haneefmubarak/satnogs-rotator/cover/cover_side_mirror.fcstd

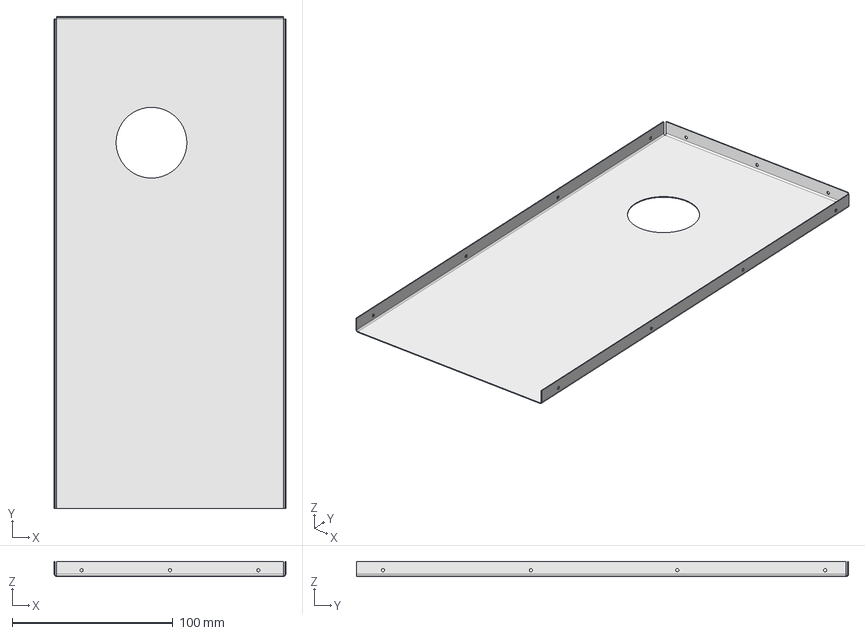
[picture p15: CAD file, 2017-07-28]
cover/cover_side_mirror.fcstd
144.0 x 306.0 x 9.50 mm
