haneefmubarak/satnogs-rotator/rotator_parts/worm_mount.fcstd

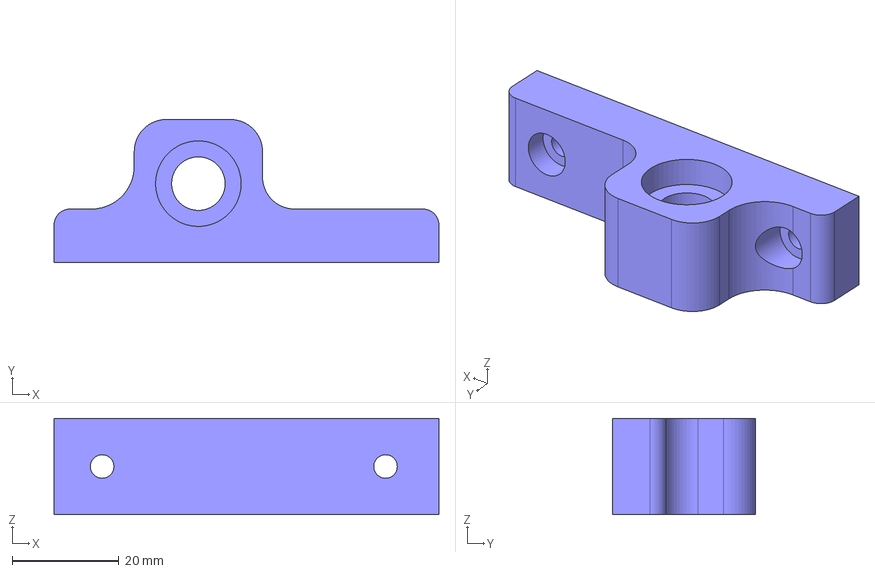
[picture p16: CAD file, 2017-07-28]
rotator_parts/worm_mount.fcstd
72.0 x 26.8 x 18.0 mm
