haneefmubarak/satnogs-rotator/shared/ball_bearing_623ZZ.fcstd

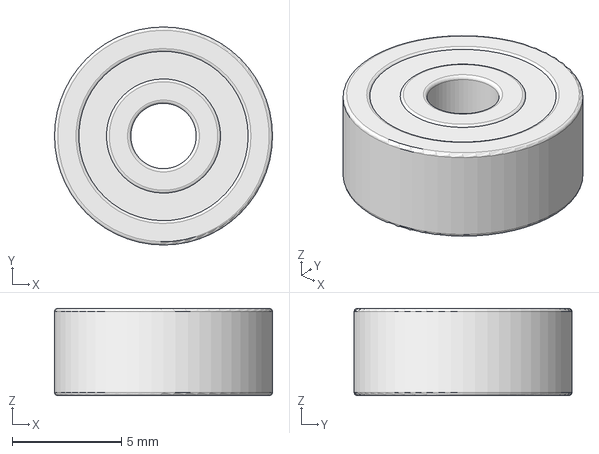
[picture p17: CAD file, 2017-07-28]
shared/ball_bearing_623ZZ.fcstd
10.0 x 10.0 x 4.00 mm
