haneefmubarak/satnogs-rotator/cover/cover_bottom.fcstd

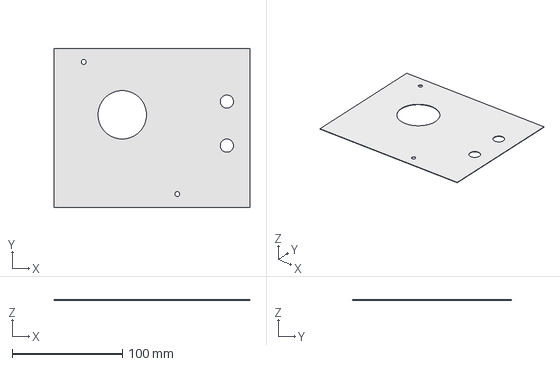
[picture p18: CAD file, 2017-07-28]
cover/cover_bottom.fcstd
178.0 x 144.0 x 0.5 mm
