haneefmubarak/satnogs-rotator/electronics/holder_as5601.fcstd

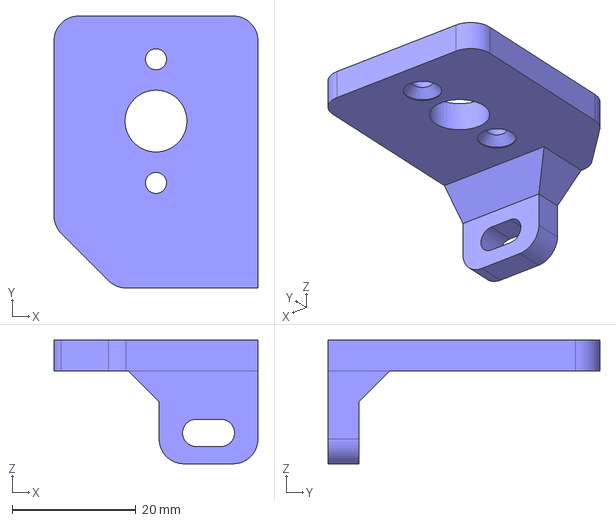
[picture p19: CAD file, 2017-07-28]
electronics/holder_as5601.fcstd
33.0 x 44.0 x 20.0 mm
