haneefmubarak/satnogs-rotator/rotator_parts/axis_gear_flange.fcstd

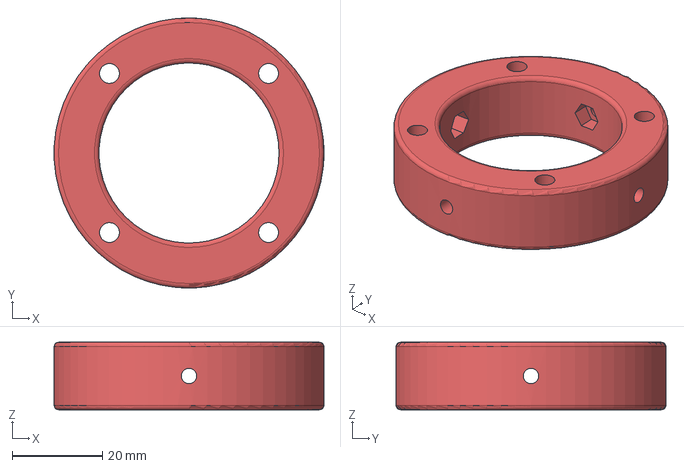
[picture p20: CAD file, 2017-07-28]
rotator_parts/axis_gear_flange.fcstd
60.0 x 60.0 x 15.0 mm
