haneefmubarak/satnogs-rotator/cover/rain_cover_tube.fcstd

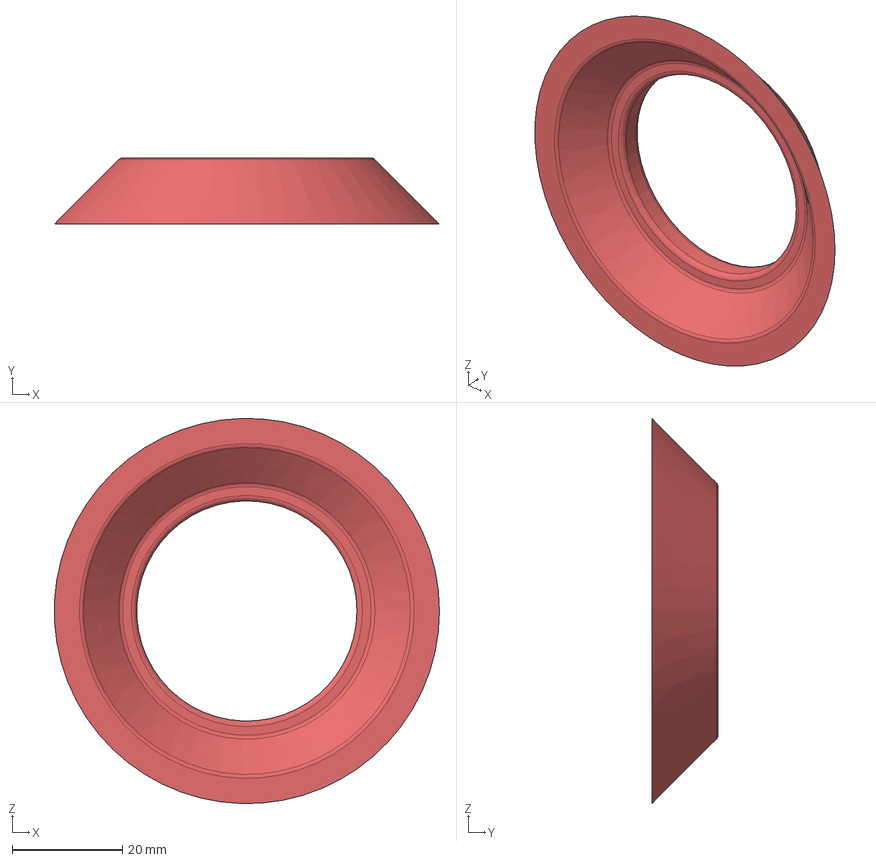
[picture p21: CAD file, 2017-07-28]
cover/rain_cover_tube.fcstd
70.0 x 12.0 x 70.0 mm
