haneefmubarak/satnogs-rotator/electronics/electronics_case_pcb_mount.fcstd

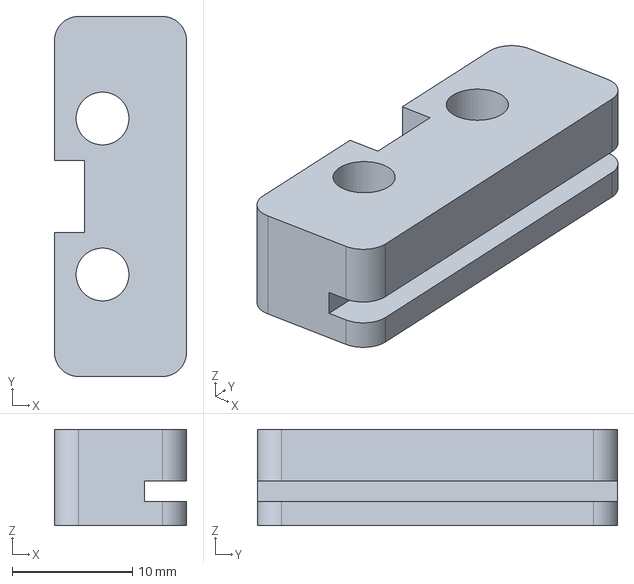
[picture p22: CAD file, 2017-07-28]
electronics/electronics_case_pcb_mount.fcstd
11.0 x 30.0 x 8.00 mm
