haneefmubarak/satnogs-rotator/rotator_parts/t_slot20_100.fcstd

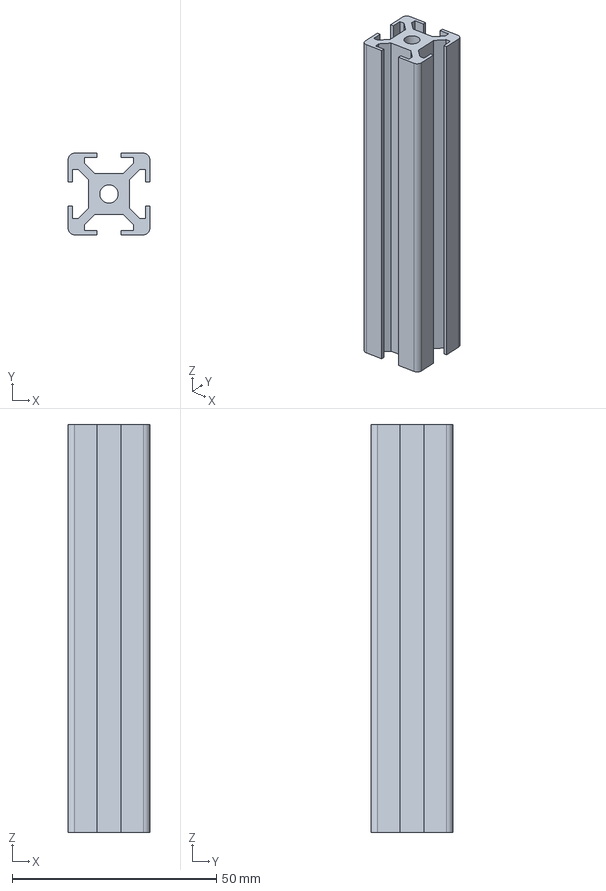
[picture p23: CAD file, 2017-07-28]
rotator_parts/t_slot20_100.fcstd
20.0 x 20.0 x 100.0 mm
