haneefmubarak/satnogs-rotator/shared/standoff_hex_nylon_M3_L10_ff.fcstd

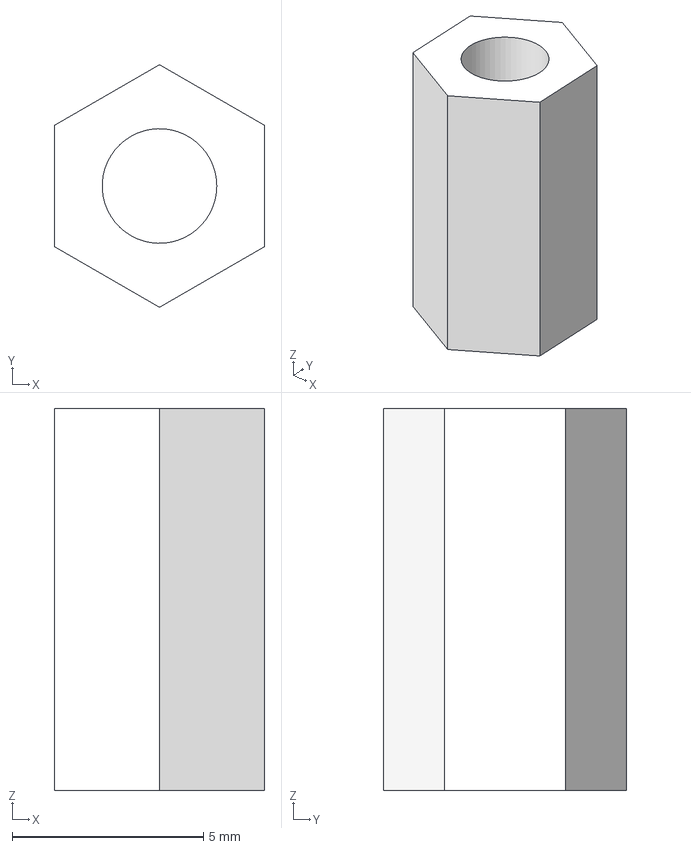
[picture p24: CAD file, 2017-07-28]
shared/standoff_hex_nylon_M3_L10_ff.fcstd
5.50 x 6.35 x 10.0 mm
