haneefmubarak/satnogs-rotator/electronics/off_axis_gear_as5601.fcstd

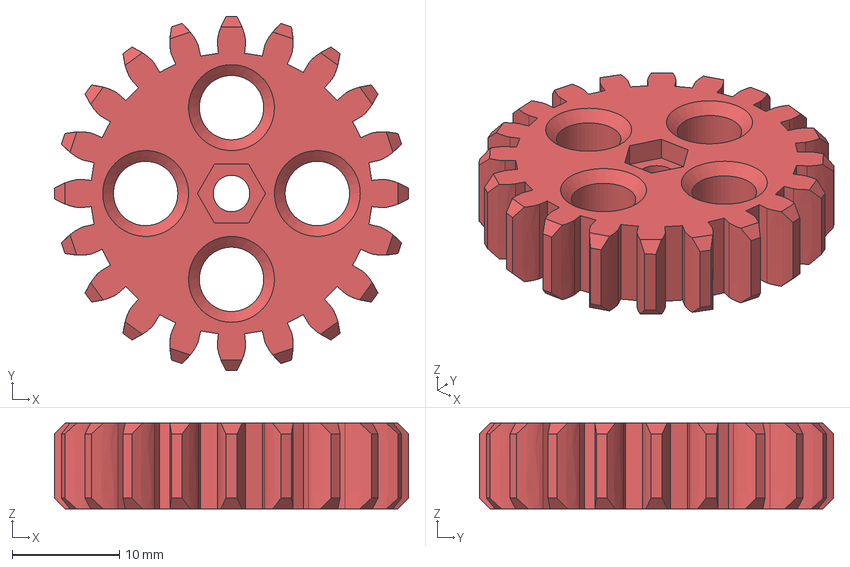
[picture p25: CAD file, 2017-07-28]
electronics/off_axis_gear_as5601.fcstd
33.0 x 33.0 x 8.00 mm
