haneefmubarak/satnogs-rotator/rotator_parts/dc_motor_cup.fcstd

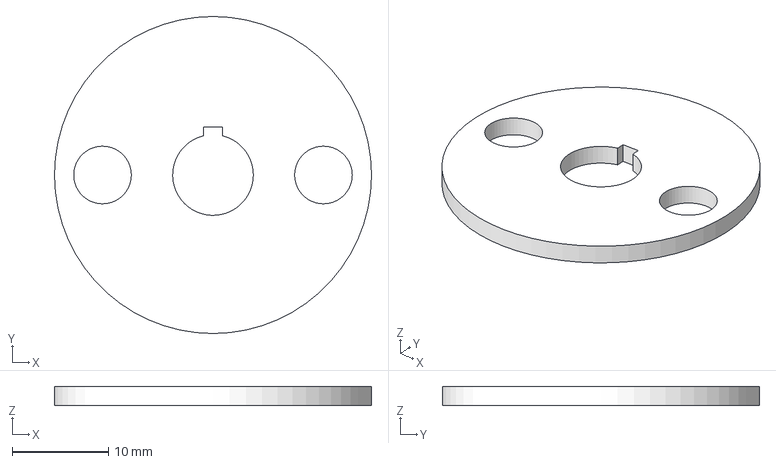
[picture p26: CAD file, 2017-07-28]
rotator_parts/dc_motor_cup.fcstd
33.0 x 33.0 x 2.00 mm
