haneefmubarak/satnogs-rotator/shared/ball_bearing_6008ZZ.fcstd

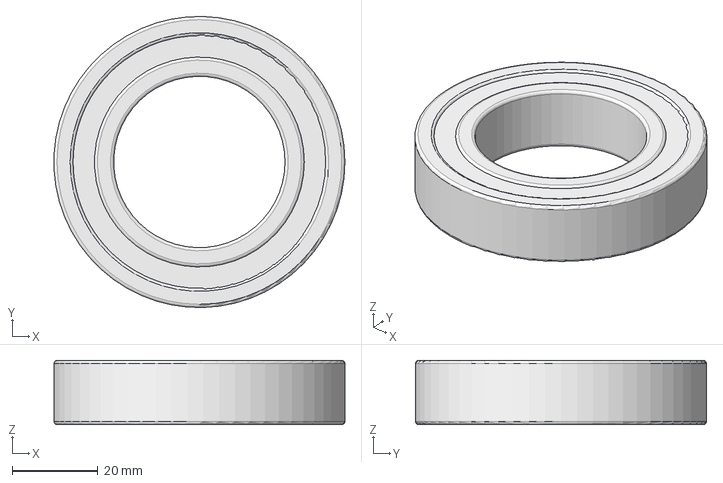
[picture p27: CAD file, 2017-07-28]
shared/ball_bearing_6008ZZ.fcstd
67.9 x 68.0 x 15.0 mm
