haneefmubarak/satnogs-rotator/electronics/encoder_magnet.fcstd

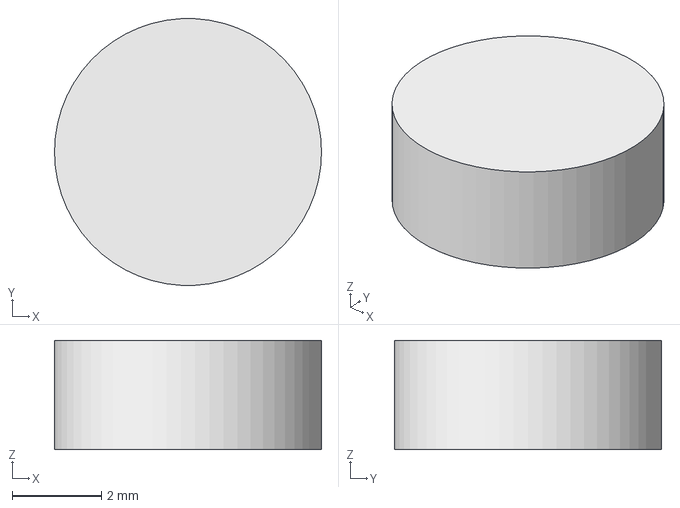
[picture p28: CAD file, 2017-07-28]
electronics/encoder_magnet.fcstd
6.00 x 5.99 x 2.45 mm
