haneefmubarak/satnogs-rotator/rotator_parts/worm_gear.fcstd

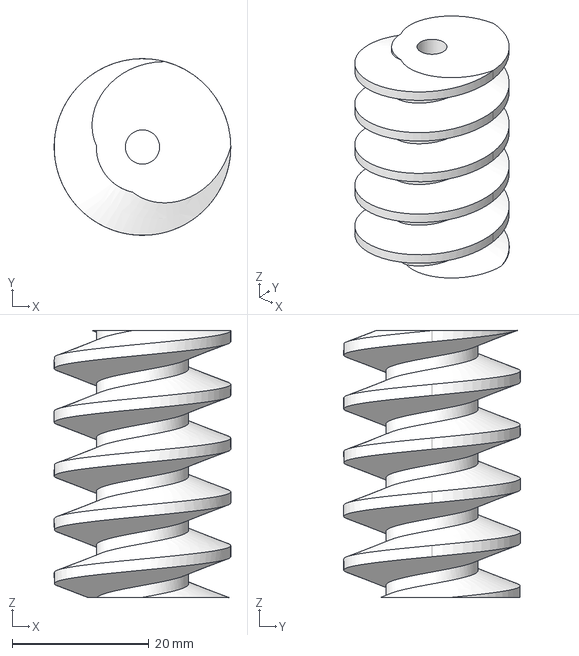
[picture p29: CAD file, 2017-07-28]
rotator_parts/worm_gear.fcstd
25.8 x 25.8 x 39.0 mm
