haneefmubarak/satnogs-rotator/shared/ball_bearing_625ZZ.fcstd

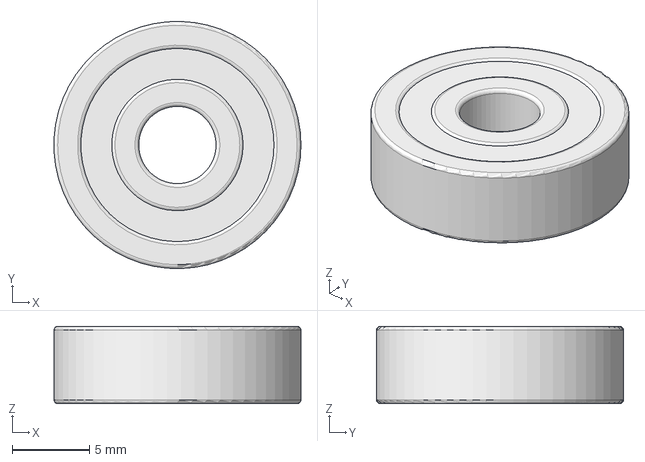
[picture p30: CAD file, 2017-07-28]
shared/ball_bearing_625ZZ.fcstd
16.0 x 16.0 x 5.00 mm
