haneefmubarak/satnogs-rotator/electronics/as5601_case_3.fcstd

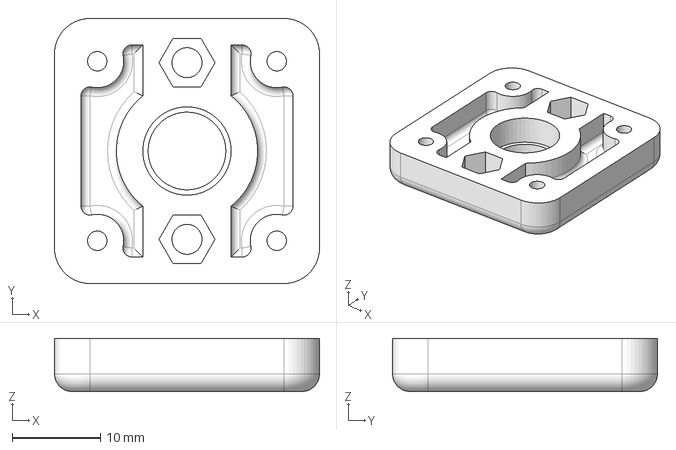
[picture p31: CAD file, 2017-07-28]
electronics/as5601_case_3.fcstd
30.0 x 30.0 x 6.00 mm
