haneefmubarak/satnogs-rotator/rotator_parts/t_slot20_connector.fcstd

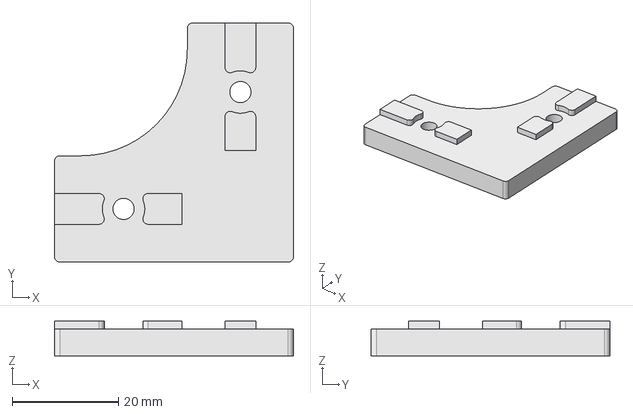
[picture p32: CAD file, 2017-07-28]
rotator_parts/t_slot20_connector.fcstd
45.0 x 45.0 x 6.50 mm
