haneefmubarak/satnogs-rotator/shared/motor_mount.fcstd

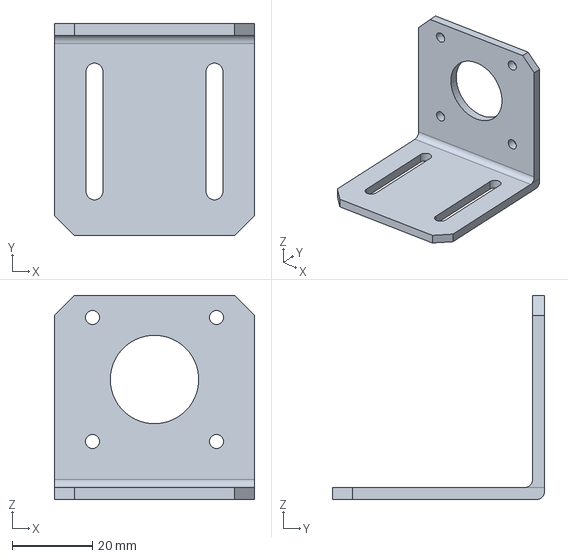
[picture p33: CAD file, 2017-07-28]
shared/motor_mount.fcstd
50.0 x 53.0 x 51.0 mm
