haneefmubarak/satnogs-rotator/electronics/as5601_pcb.fcstd

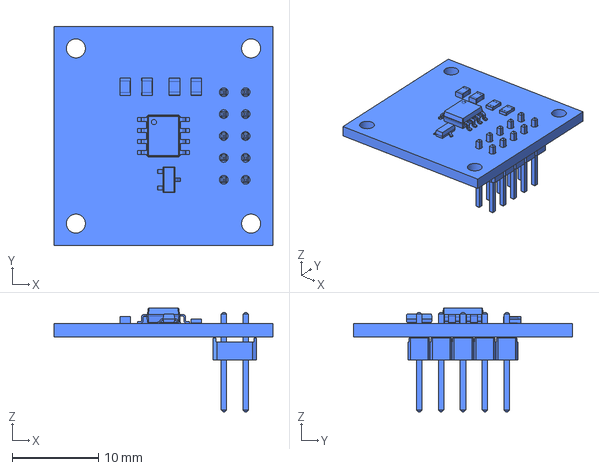
[picture p34: CAD file, 2017-07-28]
electronics/as5601_pcb.fcstd
25.4 x 25.4 x 12.0 mm
