haneefmubarak/satnogs-rotator/rotator_parts/worm_axis.fcstd

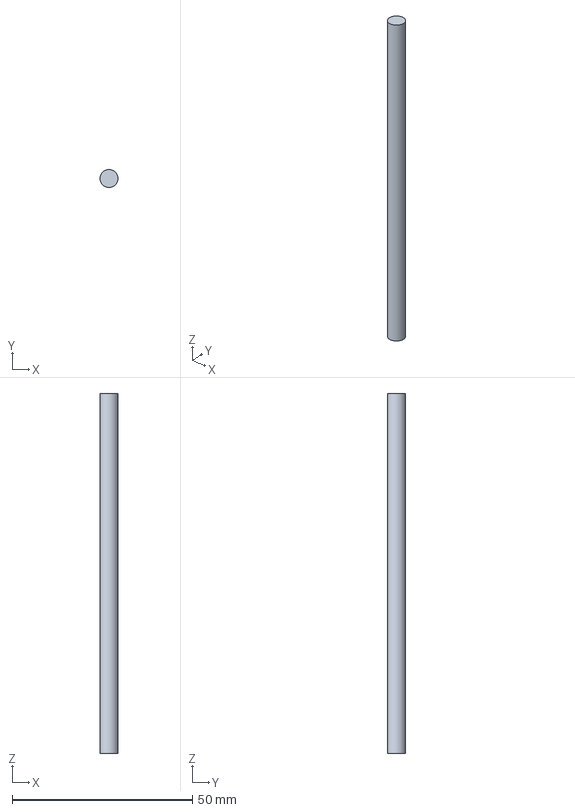
[picture p35: CAD file, 2017-07-28]
rotator_parts/worm_axis.fcstd
5.00 x 5.00 x 100.0 mm
