haneefmubarak/satnogs-rotator/shared/timing_pulley_gt2_36T.fcstd

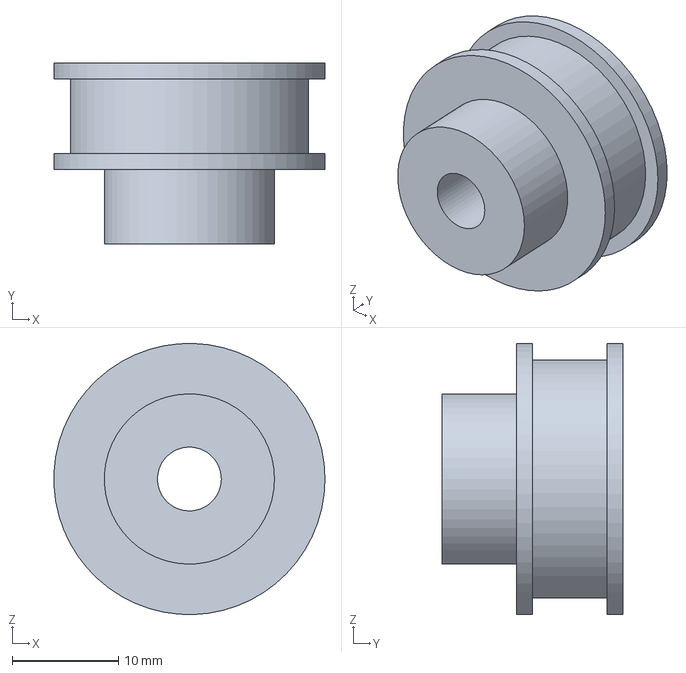
[picture p36: CAD file, 2017-07-28]
shared/timing_pulley_gt2_36T.fcstd
25.5 x 17.0 x 25.5 mm
