haneefmubarak/satnogs-rotator/rotator_parts/motor_mount_flange.fcstd

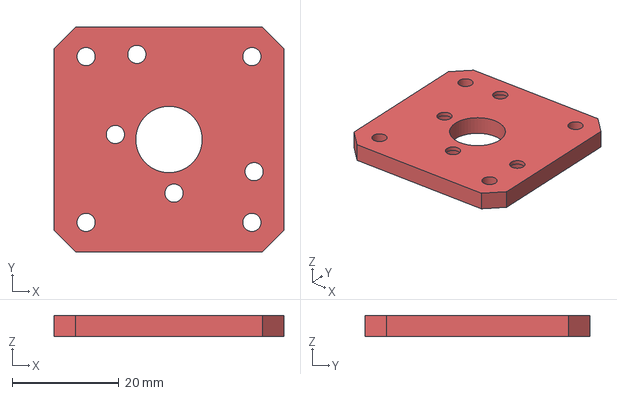
[picture p37: CAD file, 2017-07-28]
rotator_parts/motor_mount_flange.fcstd
43.0 x 42.0 x 4.00 mm
