haneefmubarak/satnogs-rotator/shared/timing_pulley_gt2_20T.fcstd

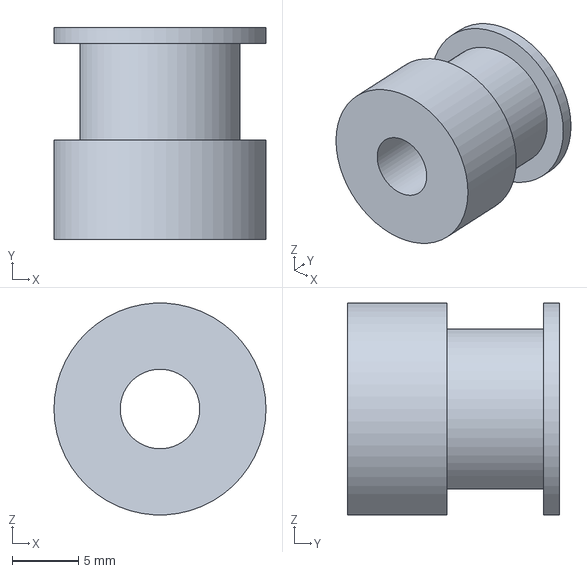
[picture p38: CAD file, 2017-07-28]
shared/timing_pulley_gt2_20T.fcstd
16.0 x 16.0 x 16.0 mm
