haneefmubarak/satnogs-rotator/electronics/as5601_case_2.fcstd

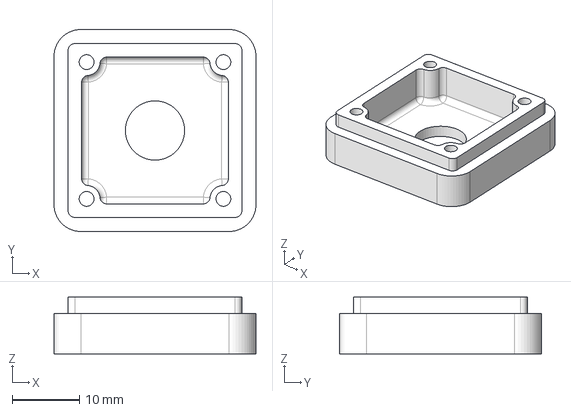
[picture p39: CAD file, 2017-07-28]
electronics/as5601_case_2.fcstd
30.0 x 30.0 x 8.40 mm
