haneefmubarak/satnogs-rotator/rotator_parts/dc_motor_heatshrink.fcstd

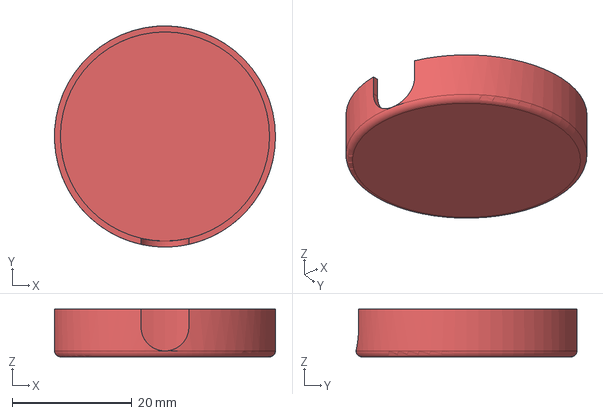
[picture p40: CAD file, 2017-07-28]
rotator_parts/dc_motor_heatshrink.fcstd
37.0 x 37.0 x 8.00 mm
