haneefmubarak/satnogs-rotator/shared/dc_motor_50:1.fcstd

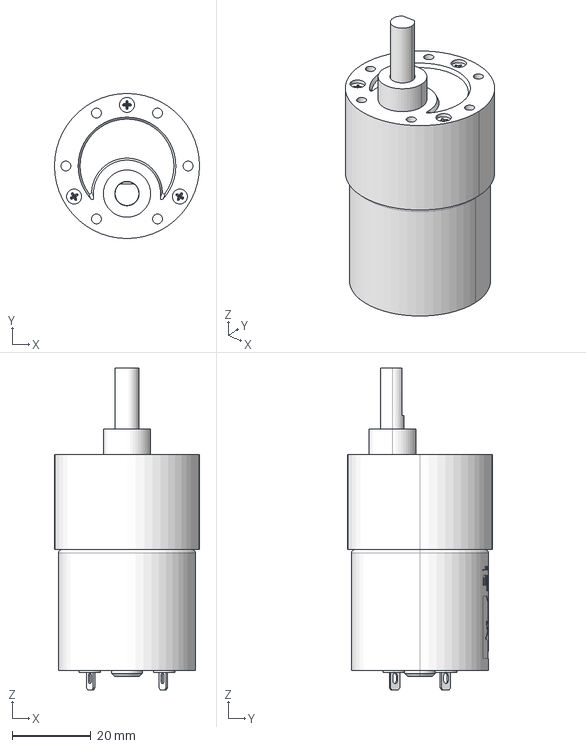
[picture p41: CAD file, 2017-07-28]
shared/dc_motor_50:1.fcstd
36.8 x 36.8 x 81.7 mm
