haneefmubarak/satnogs-rotator/electronics/electronics_case_top.fcstd

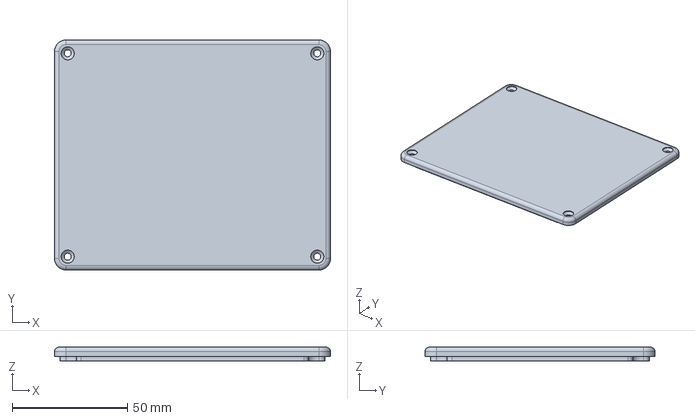
[picture p42: CAD file, 2017-07-28]
electronics/electronics_case_top.fcstd
120.0 x 100.0 x 6.00 mm
