haneefmubarak/satnogs-rotator/rotator_parts/ball_bearing_housing.fcstd

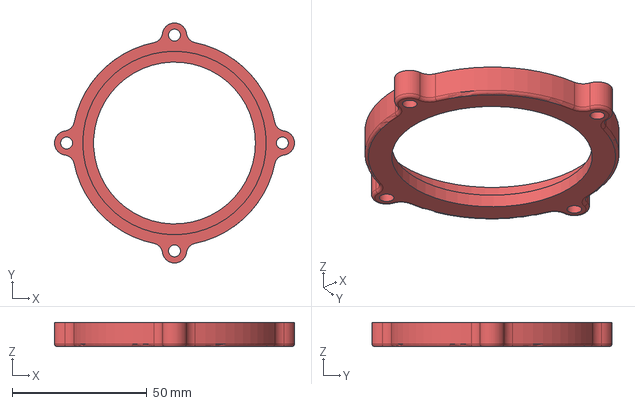
[picture p43: CAD file, 2017-07-28]
rotator_parts/ball_bearing_housing.fcstd
89.0 x 89.0 x 9.00 mm
