haneefmubarak/satnogs-rotator/electronics/as5601_magnet_base.fcstd

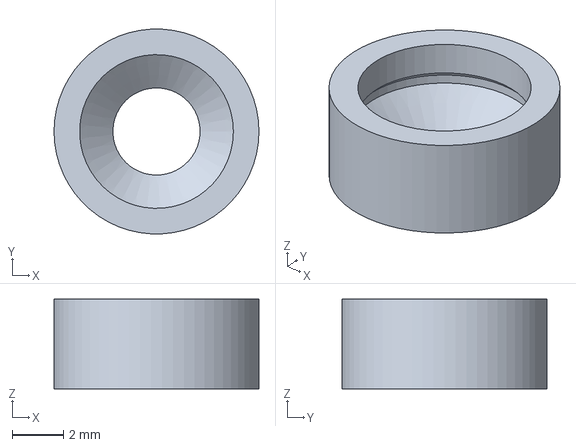
[picture p44: CAD file, 2017-07-28]
electronics/as5601_magnet_base.fcstd
8.00 x 7.99 x 3.50 mm
