haneefmubarak/satnogs-rotator/rotator_parts/switch_endstop_holder.fcstd

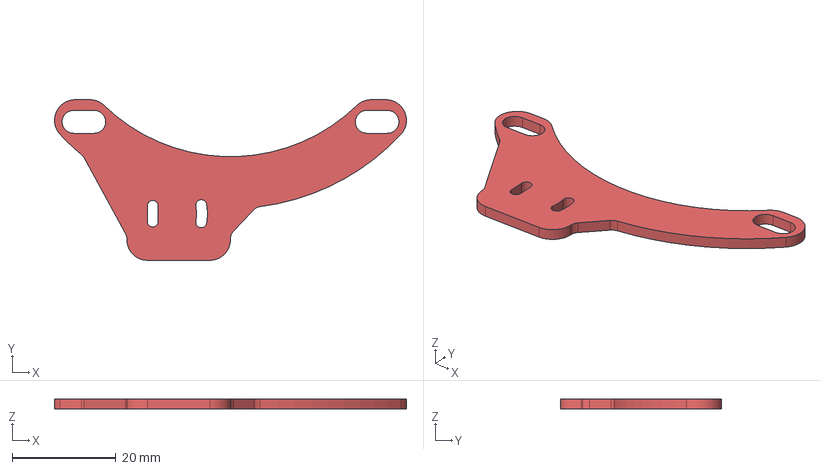
[picture p45: CAD file, 2017-07-28]
rotator_parts/switch_endstop_holder.fcstd
67.9 x 31.0 x 2.00 mm
