haneefmubarak/satnogs-rotator/shared/stepper_motor_nema17.fcstd

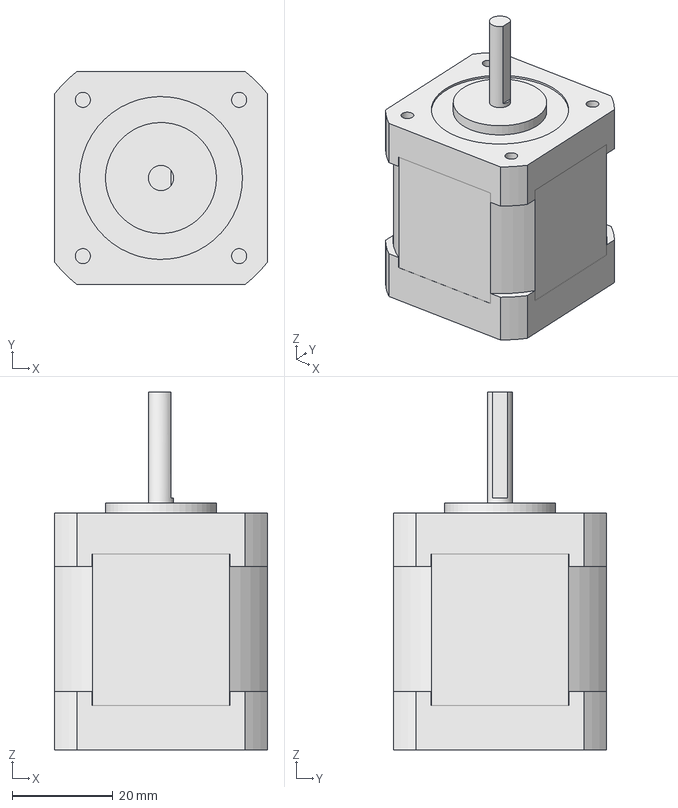
[picture p46: CAD file, 2017-07-28]
shared/stepper_motor_nema17.fcstd
42.3 x 42.3 x 71.0 mm
