haneefmubarak/satnogs-rotator/electronics/electronics_case.fcstd

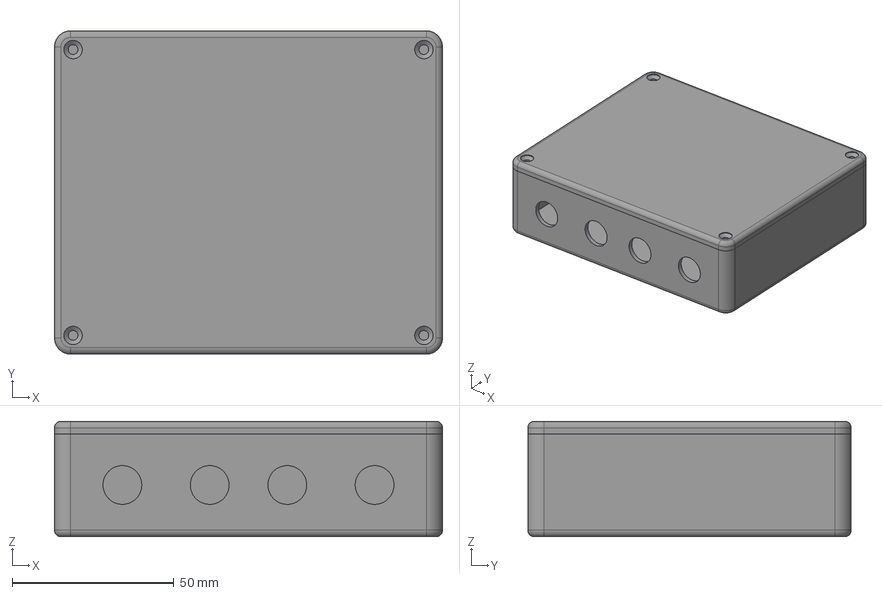
[picture p47: CAD file, 2017-07-28]
electronics/electronics_case.fcstd
120.0 x 100.0 x 35.7 mm
electronics_case_bottom_01
electronics_case_pcb_mount_01
electronics_case_pcb_mount_02
electronics_case_top_01
