haneefmubarak/satnogs-rotator/rotator_parts/homing_ring.fcstd

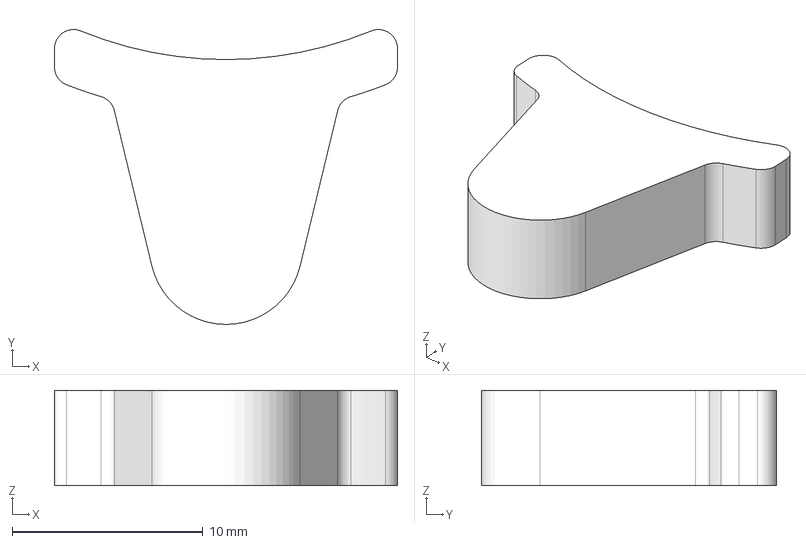
[picture p48: CAD file, 2017-07-28]
rotator_parts/homing_ring.fcstd
18.0 x 15.5 x 5.00 mm
