haneefmubarak/satnogs-rotator/electronics/electronics_case_bottom.fcstd

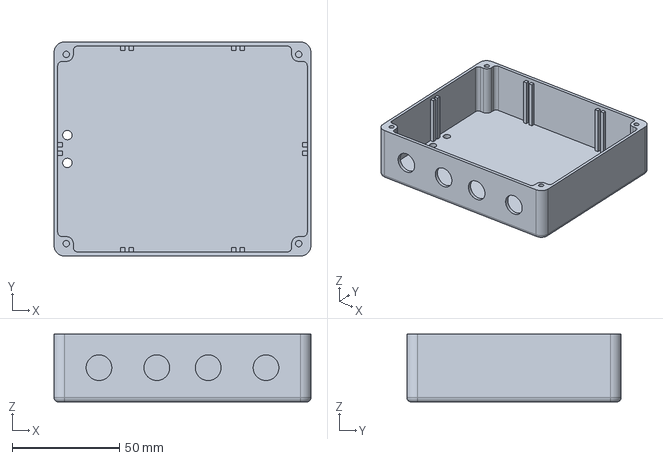
[picture p49: CAD file, 2017-07-28]
electronics/electronics_case_bottom.fcstd
120.0 x 100.0 x 31.7 mm
