haneefmubarak/satnogs-rotator/rotator_parts/t_slot20_160.fcstd

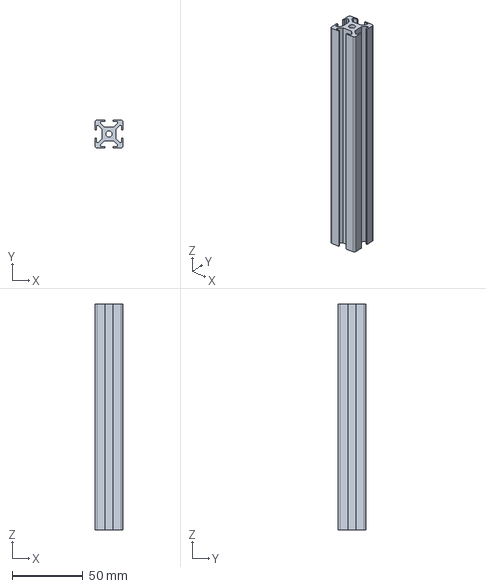
[picture p50: CAD file, 2017-07-28]
rotator_parts/t_slot20_160.fcstd
20.0 x 20.0 x 160.0 mm
