haneefmubarak/satnogs-rotator/shared/Inner_bracket_20_steel_B-Type_slot6.fcstd

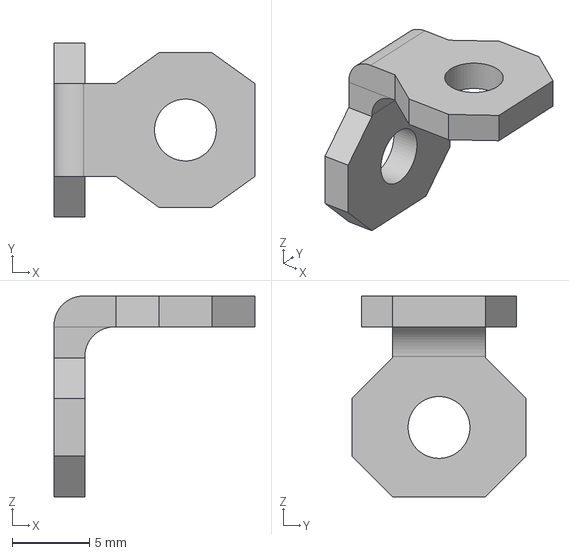
[picture p51: CAD file, 2017-07-28]
shared/Inner_bracket_20_steel_B-Type_slot6.fcstd
13.0 x 11.3 x 13.0 mm
