haneefmubarak/satnogs-rotator/rotator_parts/axis_side.fcstd

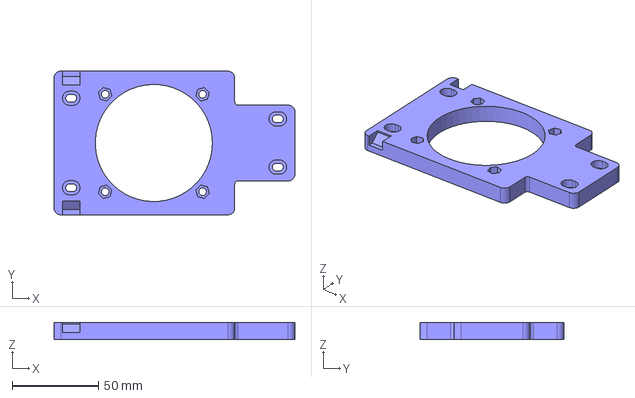
[picture p52: CAD file, 2017-07-28]
rotator_parts/axis_side.fcstd
140.0 x 83.5 x 10.0 mm
