haneefmubarak/satnogs-rotator/rotator_parts/axis_pipe_40mm.fcstd

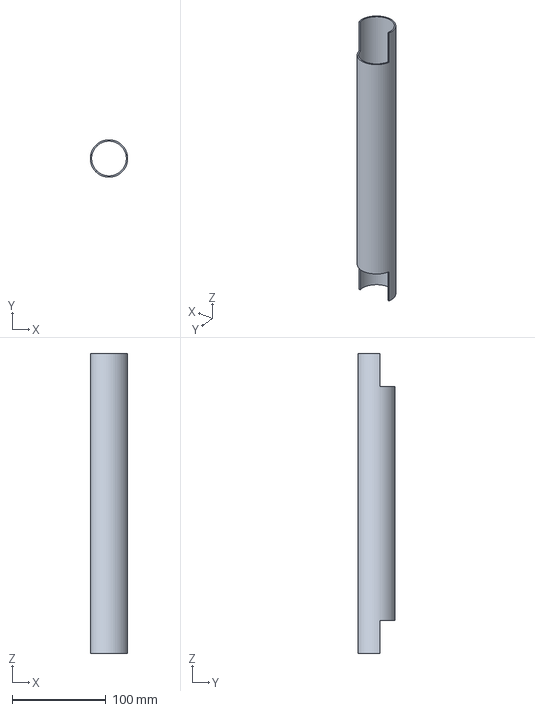
[picture p53: CAD file, 2017-07-28]
rotator_parts/axis_pipe_40mm.fcstd
40.0 x 40.0 x 320.0 mm
