haneefmubarak/satnogs-rotator/rotator_parts/motor_mount_plastic.fcstd

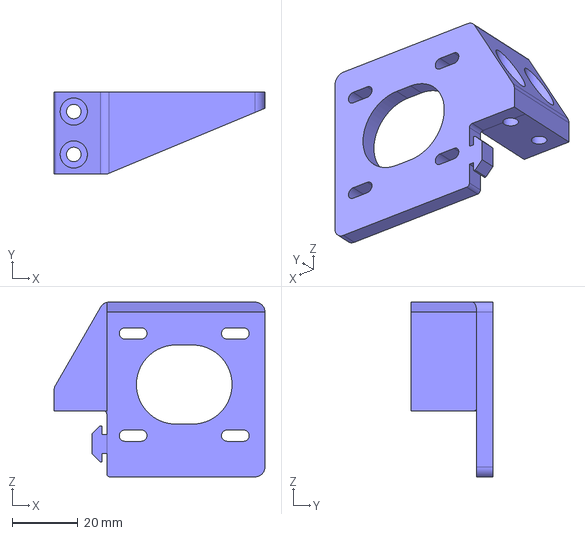
[picture p54: CAD file, 2017-07-28]
rotator_parts/motor_mount_plastic.fcstd
64.0 x 25.0 x 53.0 mm
